geryx14/Water-Monitoring-System/Scematic Hardwere/Wiring Panel Box ESP32.png

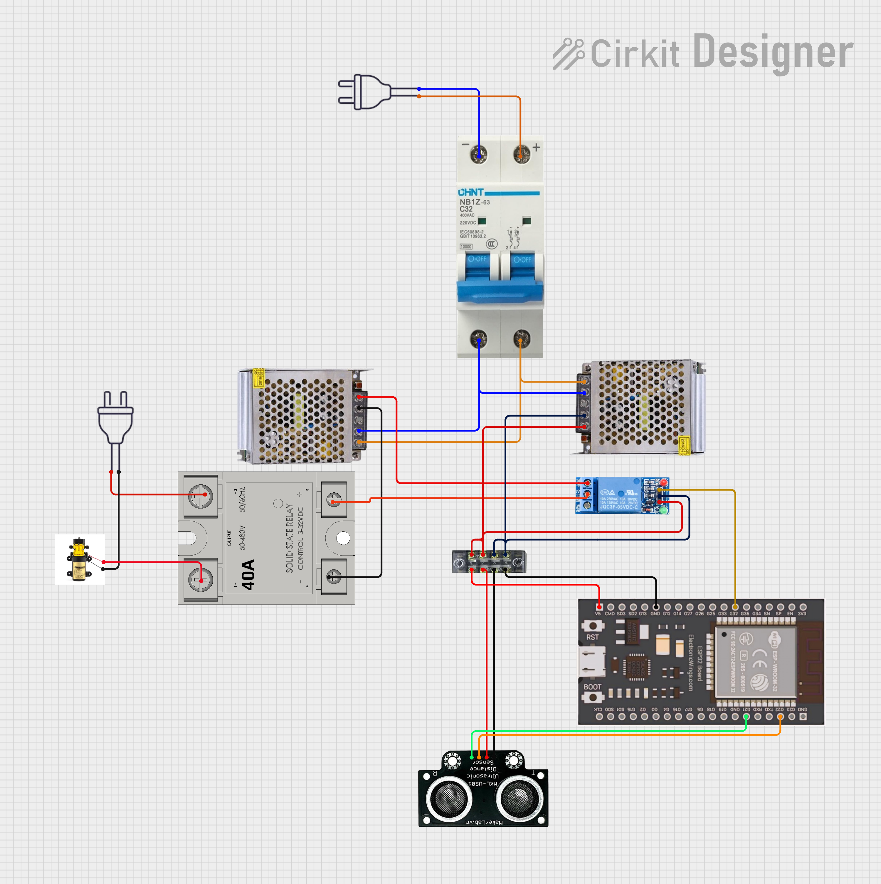
Scematic Hardwere/Wiring Panel Box ESP32.png
