geryx14/Water-Monitoring-System/Scematic Hardwere/Wiring Panel Box Raspi.png

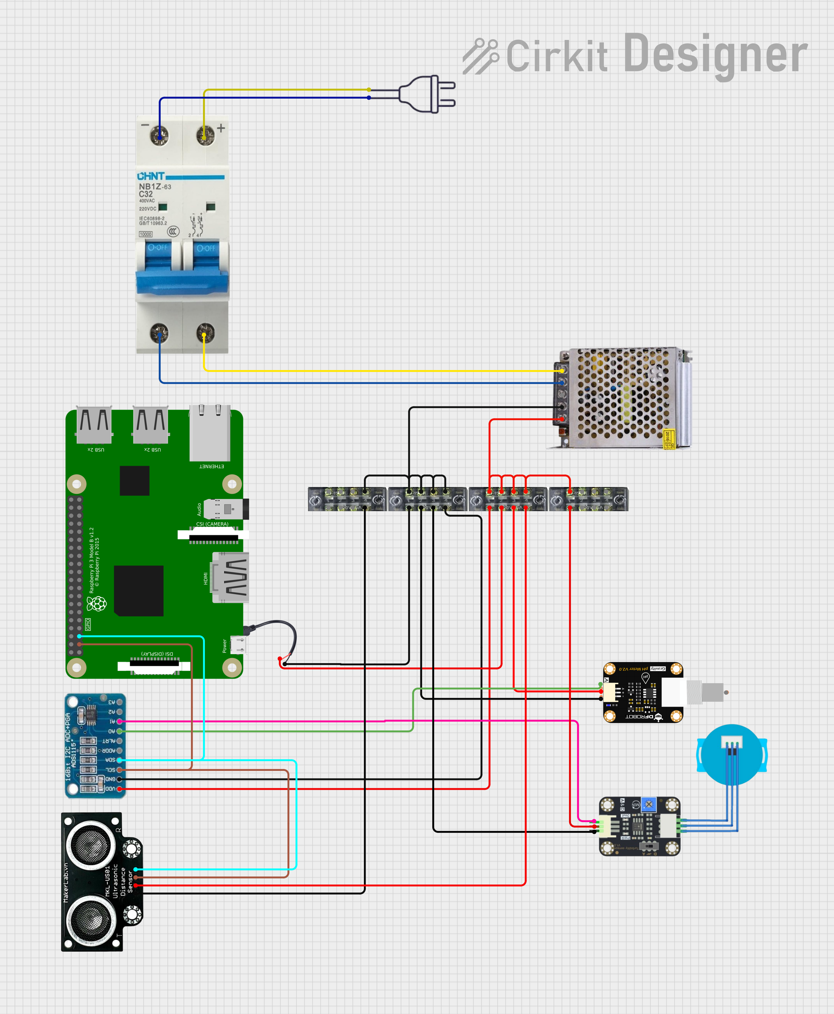
Scematic Hardwere/Wiring Panel Box Raspi.png
