geryx14/Water-Monitoring-System/Scematic Hardwere/Wiring Raspi.png

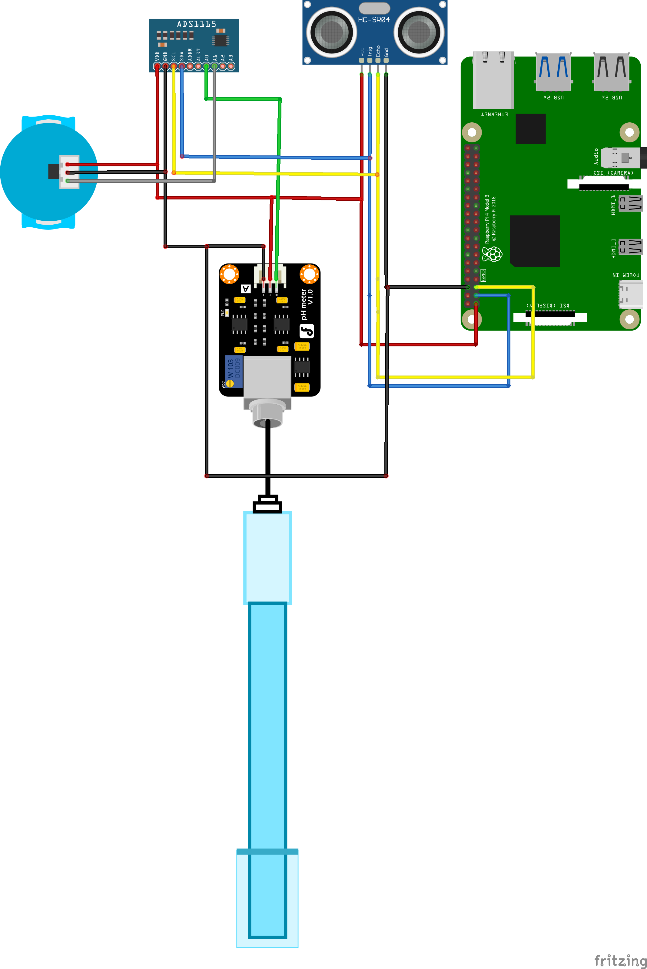
Scematic Hardwere/Wiring Raspi.png
